dmvo/ecgpatch/ios/ECG/Pysty_stop.png

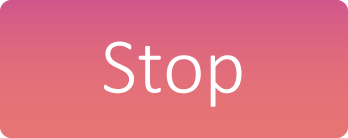
ios/ECG/Pysty_stop.png
